muntedpissmole/pccs5/images/ipad_glassmorphism_dark_home_portrait.png

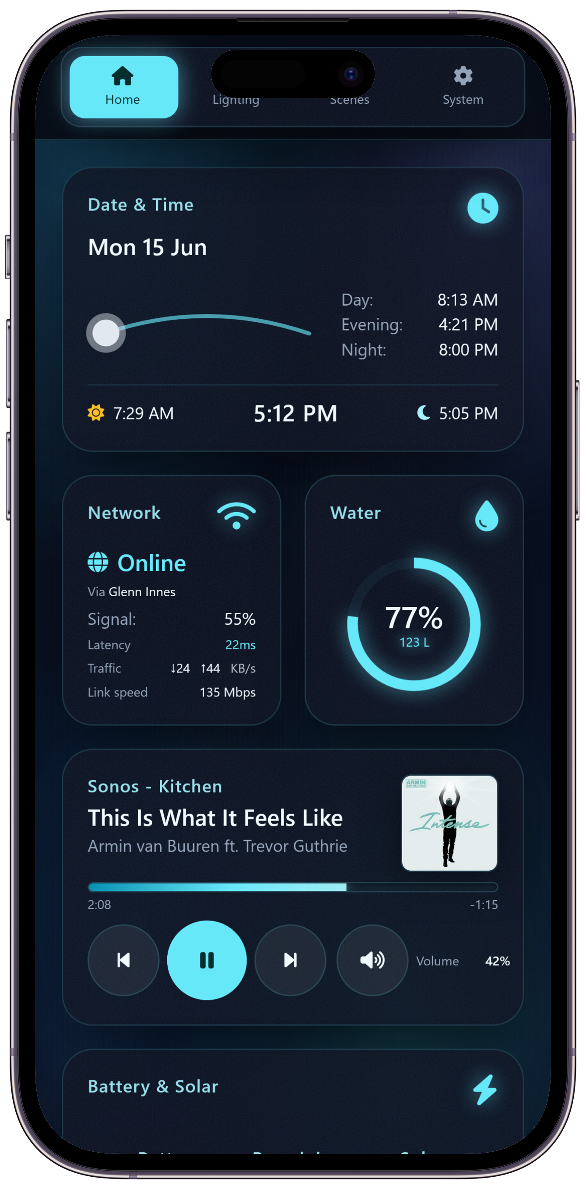
images/ipad_glassmorphism_dark_home_portrait.png
