muntedpissmole/pccs5/images/ipad_glassmorphism_light_home_landscape.png

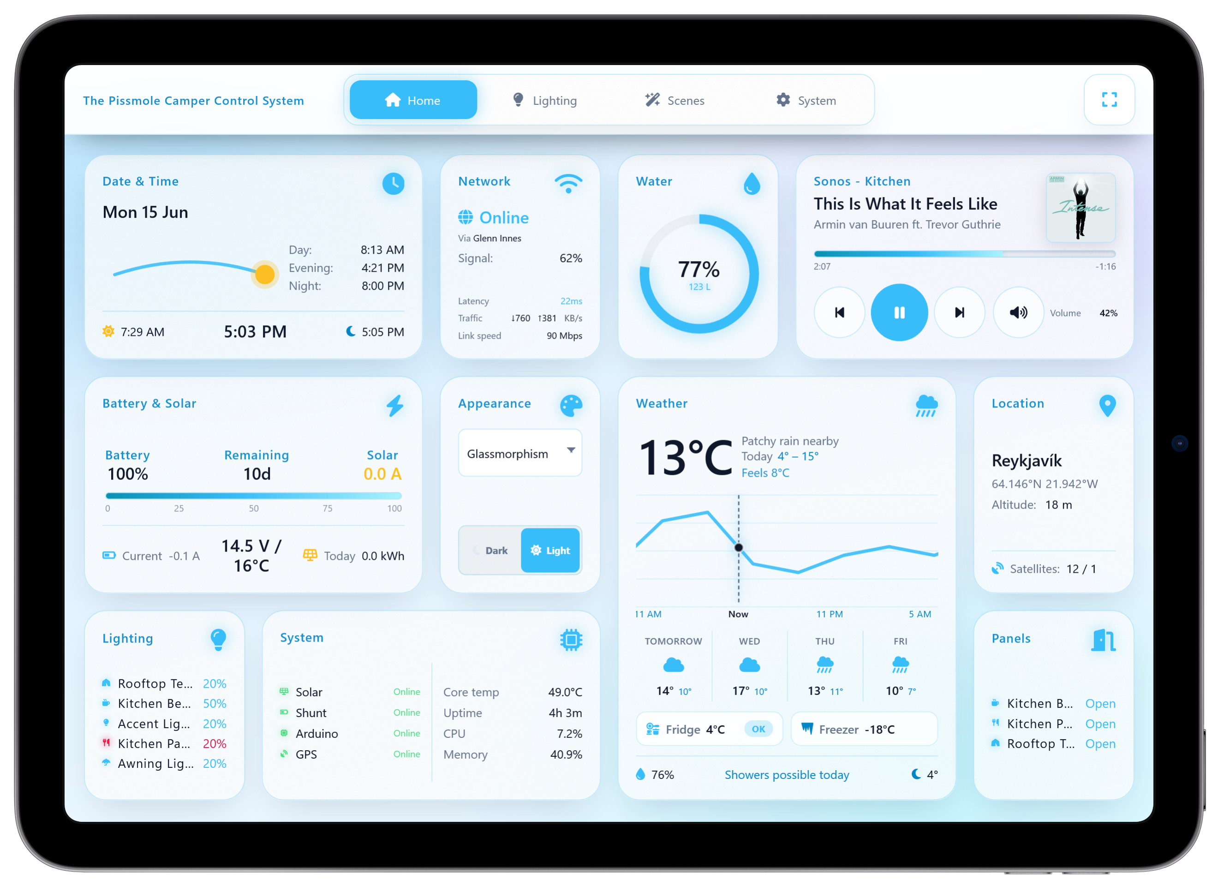
images/ipad_glassmorphism_light_home_landscape.png
