muntedpissmole/pccs5/images/ipad_glassmorphism_light_lighting_landscape.png

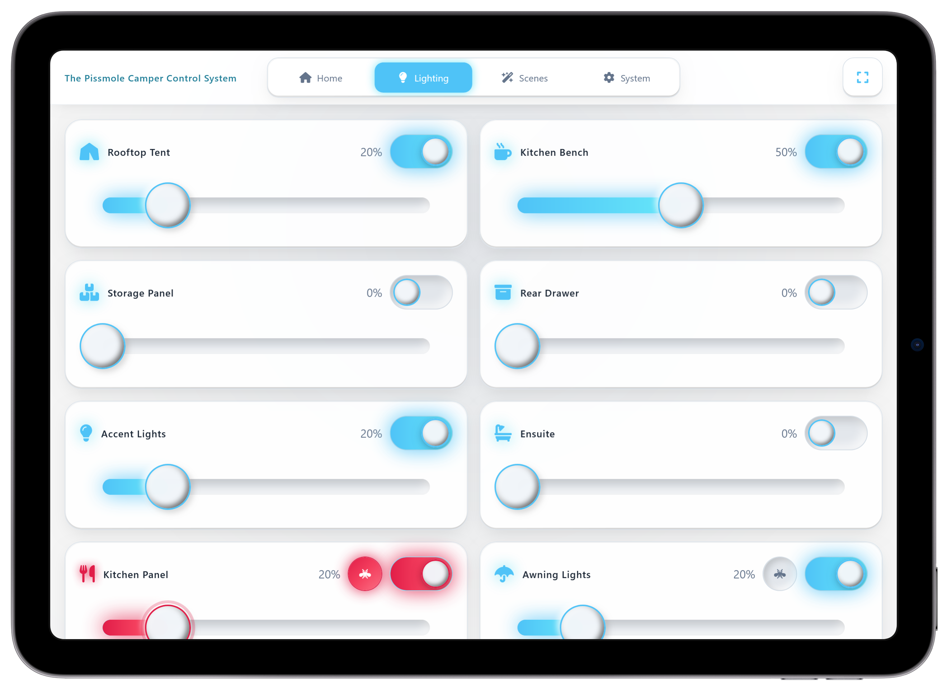
images/ipad_glassmorphism_light_lighting_landscape.png
