muntedpissmole/pccs5/images/ipad_neumorphism_dark_system_landscape.png

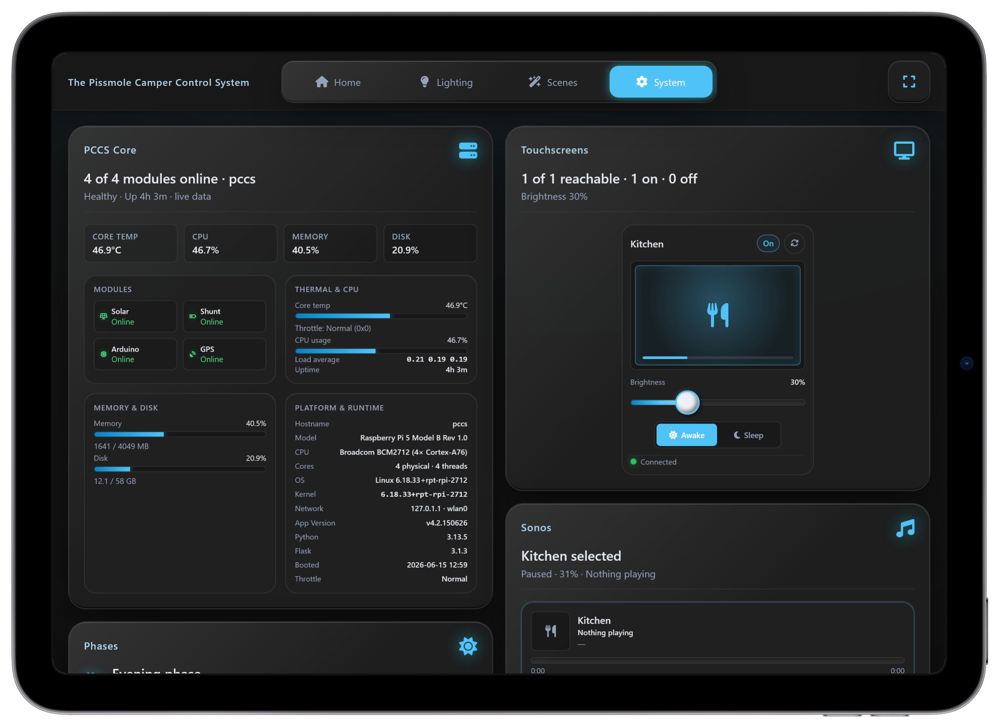
images/ipad_neumorphism_dark_system_landscape.png
