muntedpissmole/pccs5/images/themes/Claymorphism/Screen Shot 2026-06-15 at 17.03.54.png

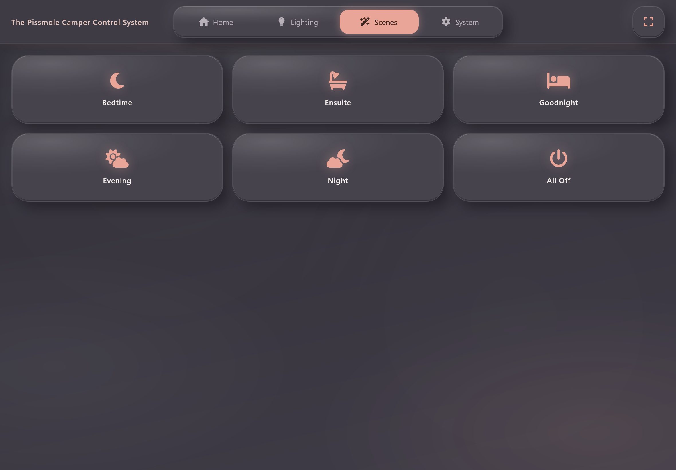
images/themes/Claymorphism/Screen Shot 2026-06-15 at 17.03.54.png
