muntedpissmole/pccs5/images/themes/Cyberpunk/Screen Shot 2026-06-15 at 17.04.39.png

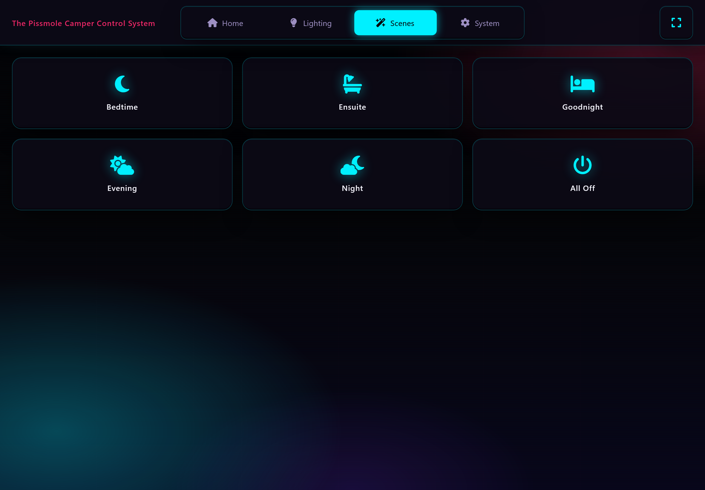
images/themes/Cyberpunk/Screen Shot 2026-06-15 at 17.04.39.png
