muntedpissmole/pccs5/images/themes/Ember/Screen Shot 2026-06-15 at 17.05.40.png

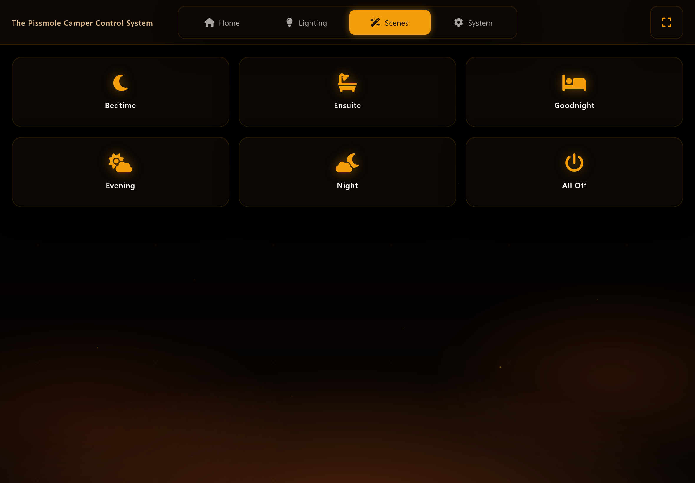
images/themes/Ember/Screen Shot 2026-06-15 at 17.05.40.png
