muntedpissmole/pccs5/images/themes/Glassmorphism/Screen Shot 2026-06-15 at 17.03.24.png

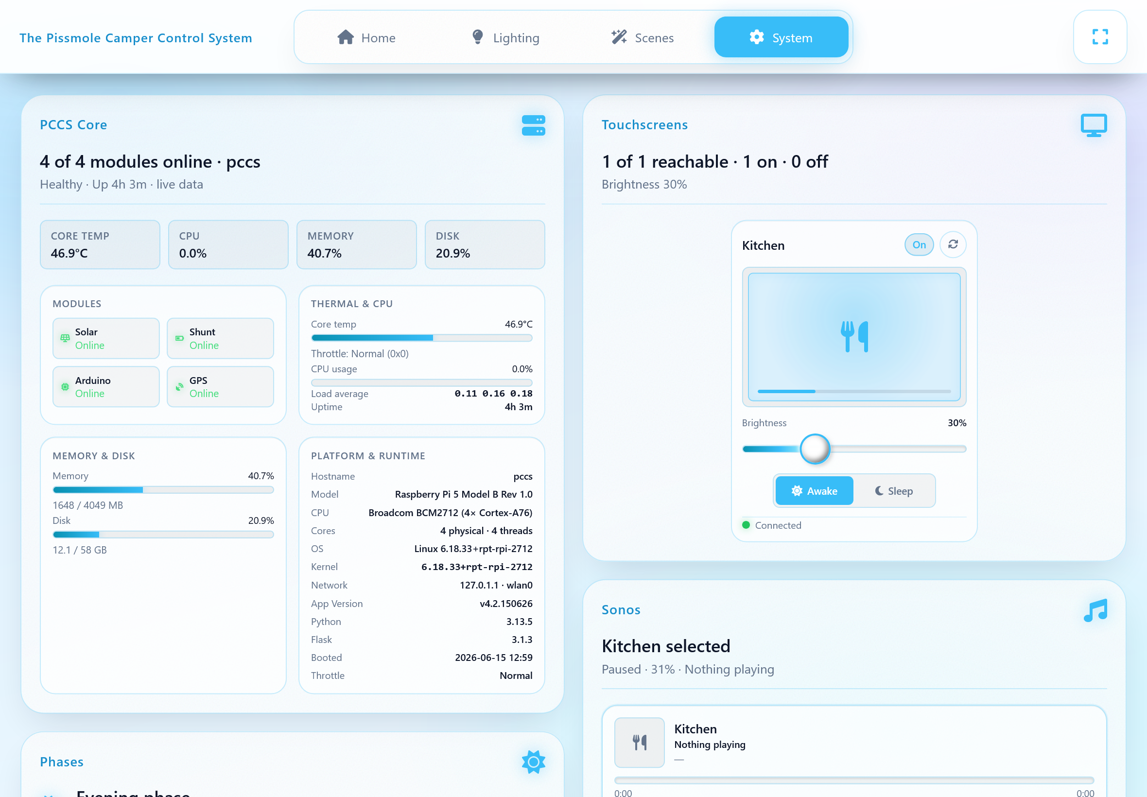
images/themes/Glassmorphism/Screen Shot 2026-06-15 at 17.03.24.png
