muntedpissmole/pccs5/images/themes/Industrial/Screen Shot 2026-06-15 at 17.06.28.png

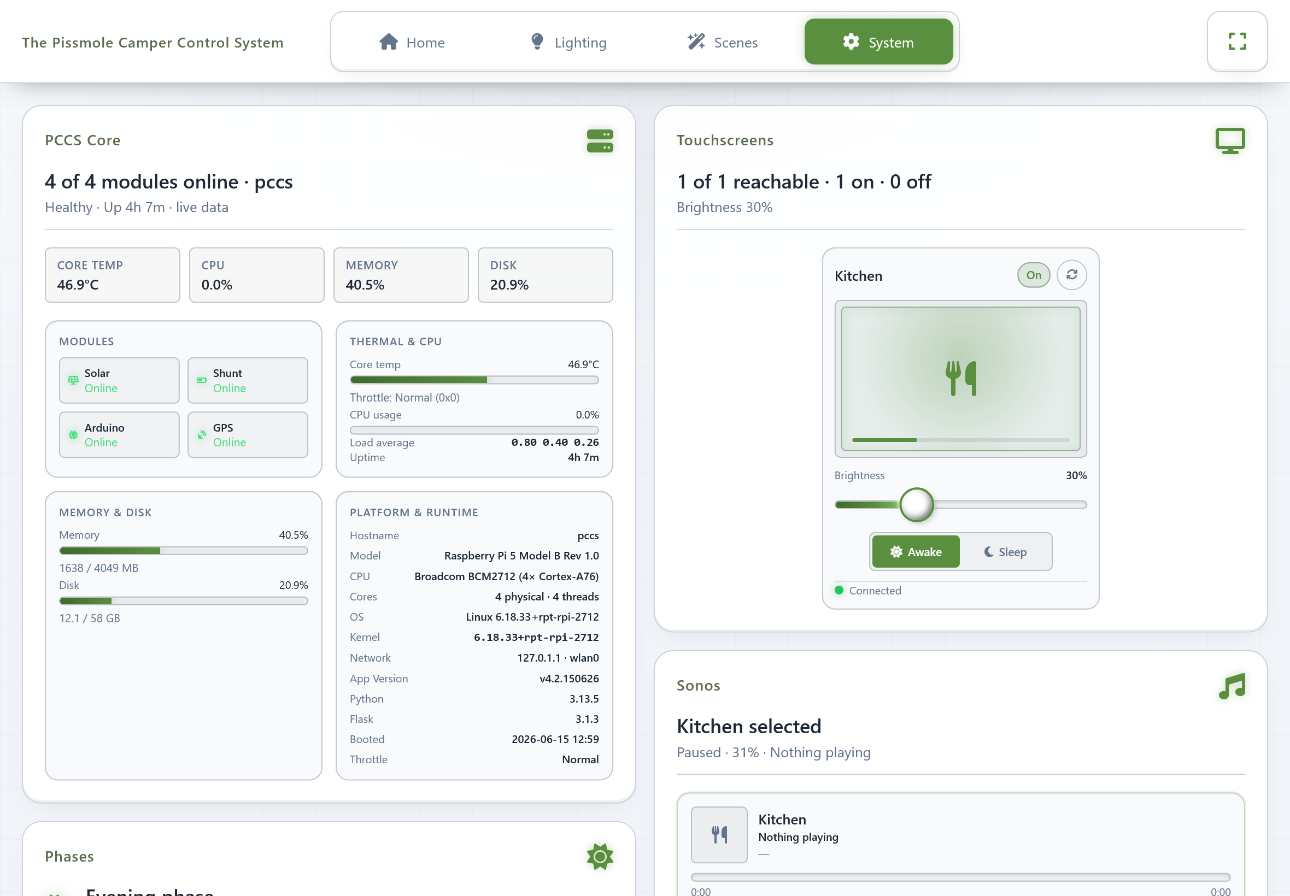
images/themes/Industrial/Screen Shot 2026-06-15 at 17.06.28.png
