muntedpissmole/pccs5/images/themes/Nebula/Screen Shot 2026-06-15 at 17.06.52.png

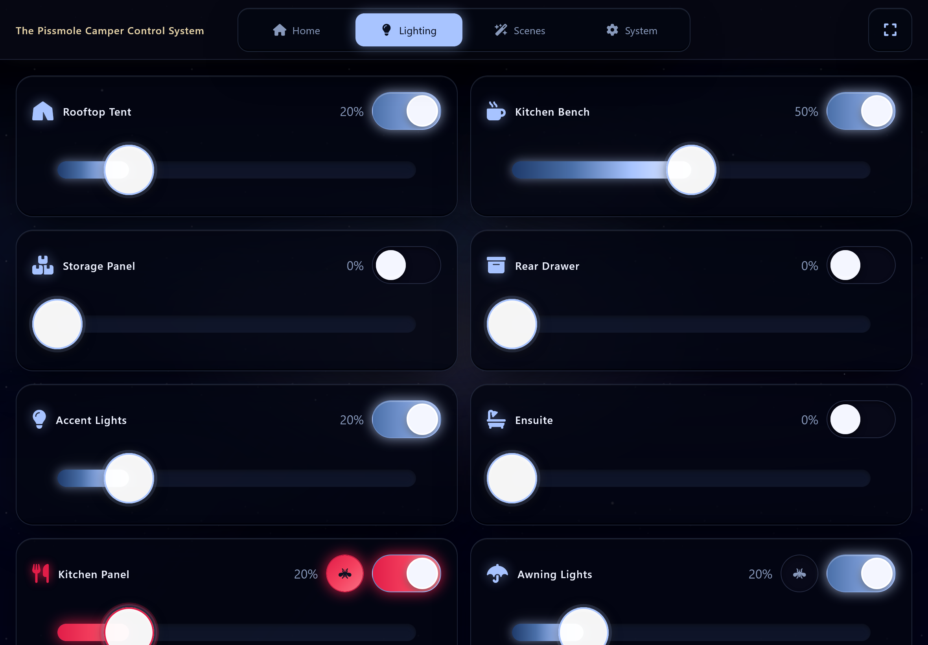
images/themes/Nebula/Screen Shot 2026-06-15 at 17.06.52.png
