muntedpissmole/pccs5/images/themes/Nebula/Screen Shot 2026-06-15 at 17.07.05.png

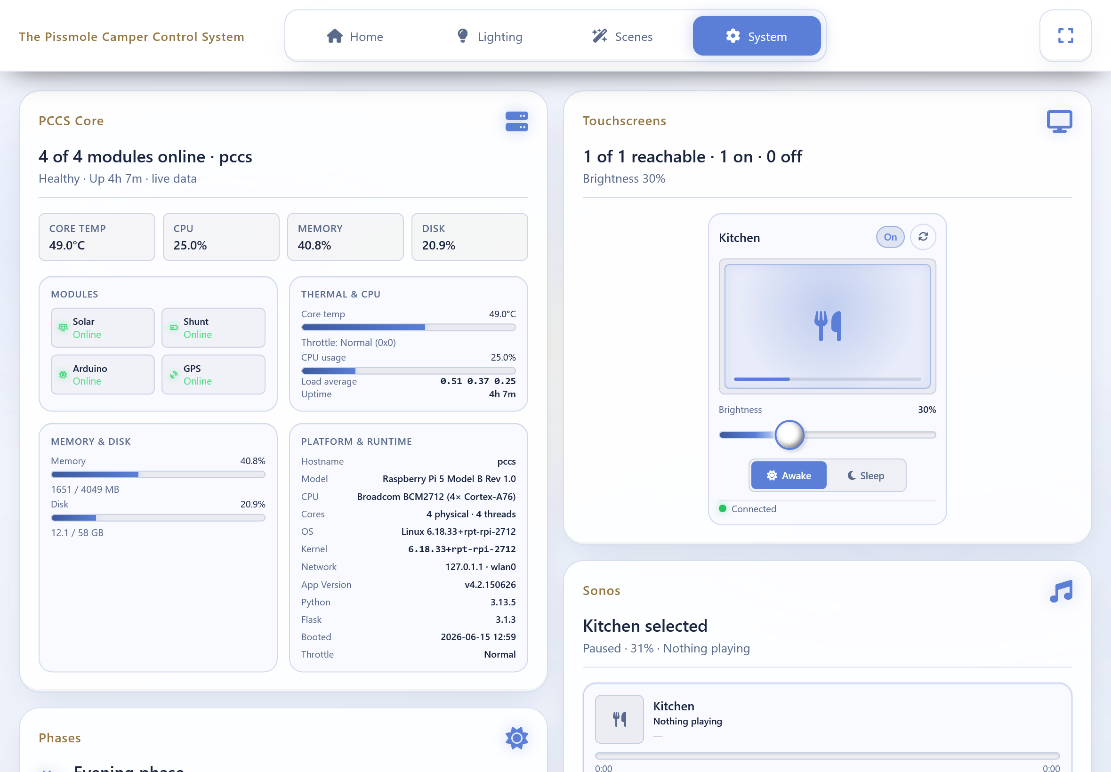
images/themes/Nebula/Screen Shot 2026-06-15 at 17.07.05.png
