muntedpissmole/pccs5/images/themes/Neumorphism/Screen Shot 2026-06-15 at 17.02.20.png

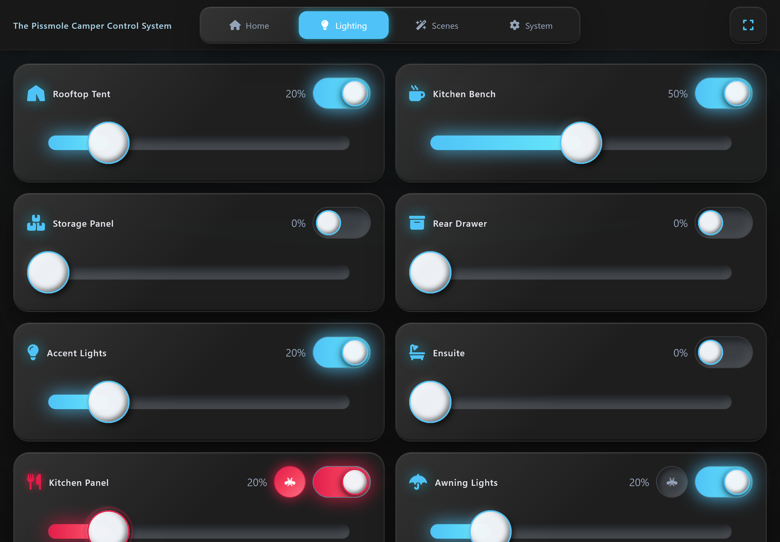
images/themes/Neumorphism/Screen Shot 2026-06-15 at 17.02.20.png
