muntedpissmole/pccs5/images/themes/Obsidian/Screen Shot 2026-06-15 at 17.07.49.png

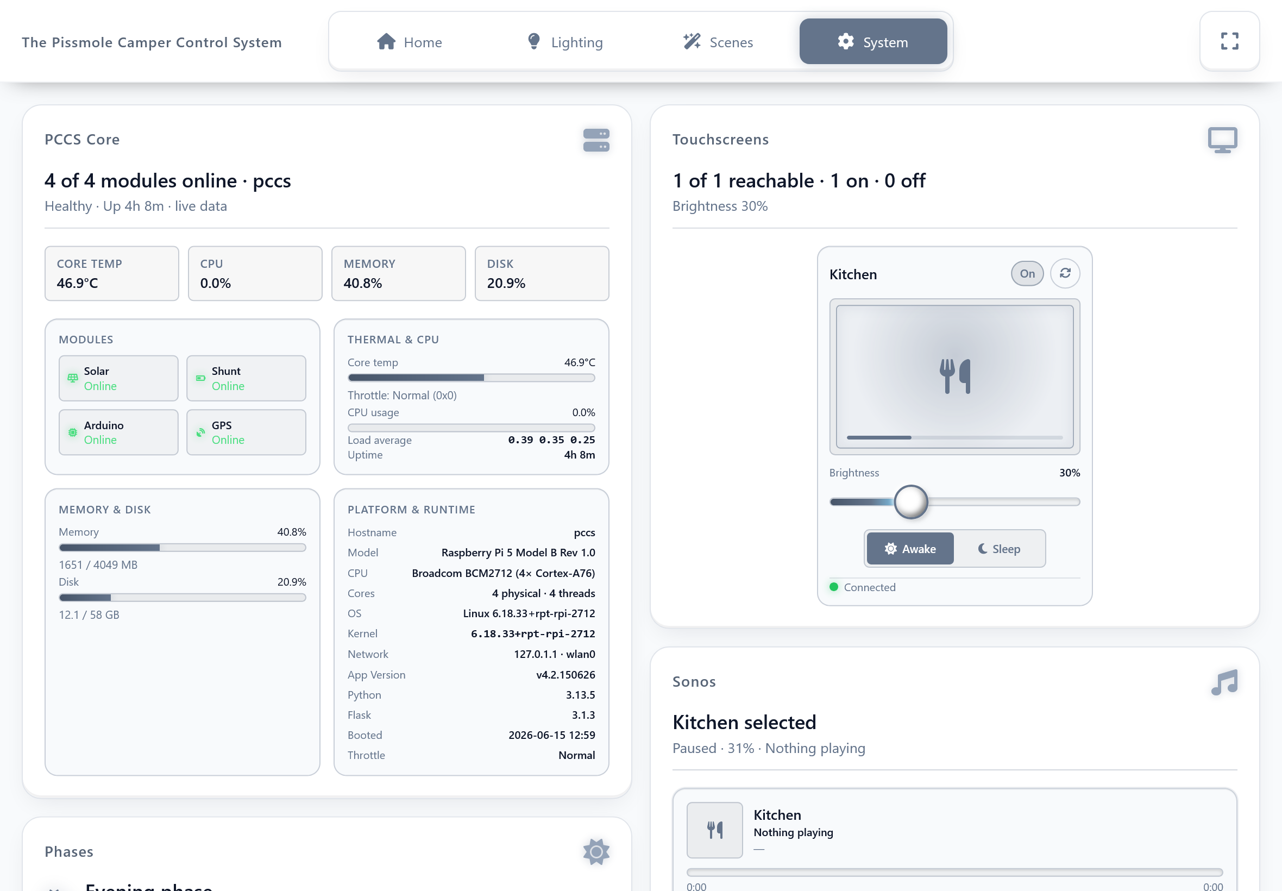
images/themes/Obsidian/Screen Shot 2026-06-15 at 17.07.49.png
