muntedpissmole/pccs5/images/themes/Terminal/Screen Shot 2026-06-15 at 17.09.07.png

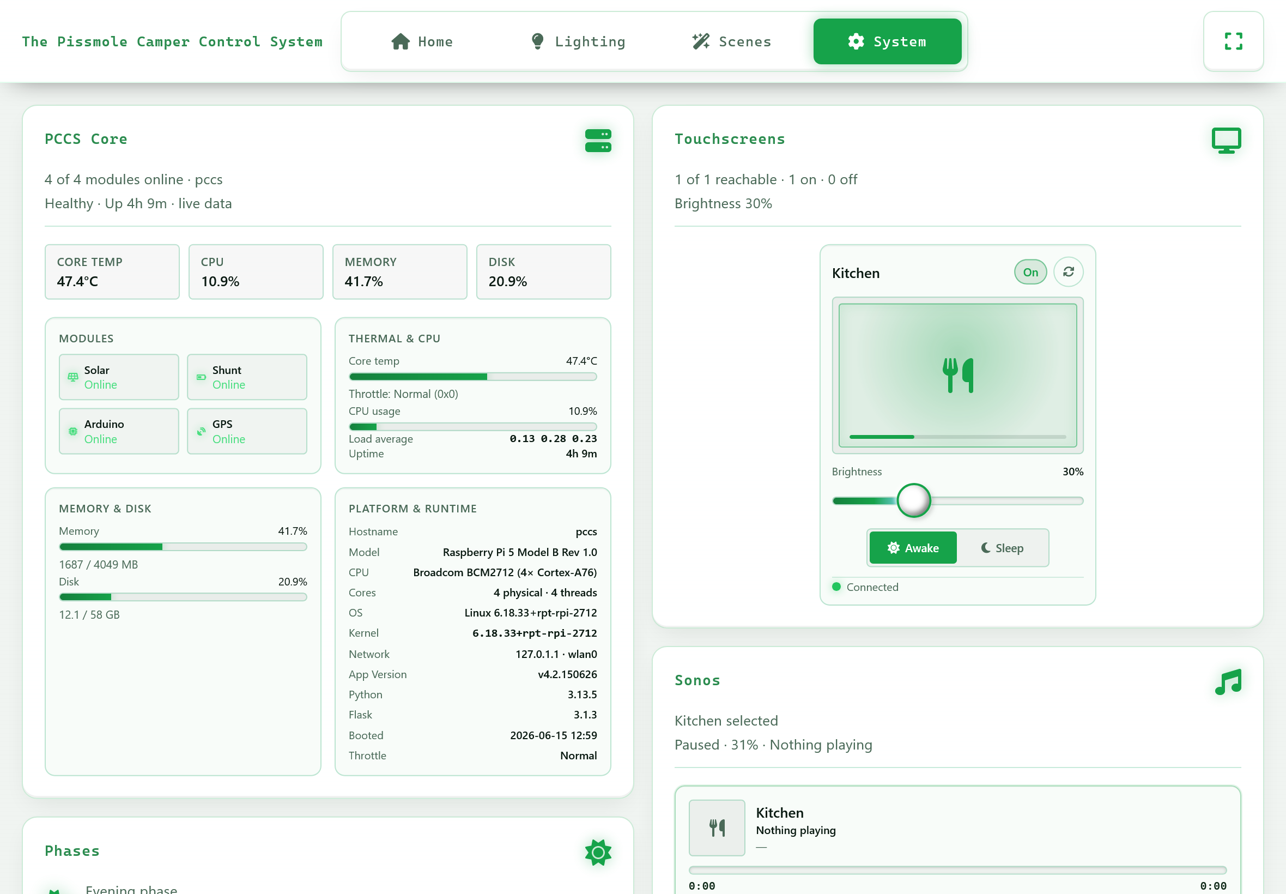
images/themes/Terminal/Screen Shot 2026-06-15 at 17.09.07.png
