muntedpissmole/pccs5/images/themes/Void/Screen Shot 2026-06-15 at 17.09.32.png

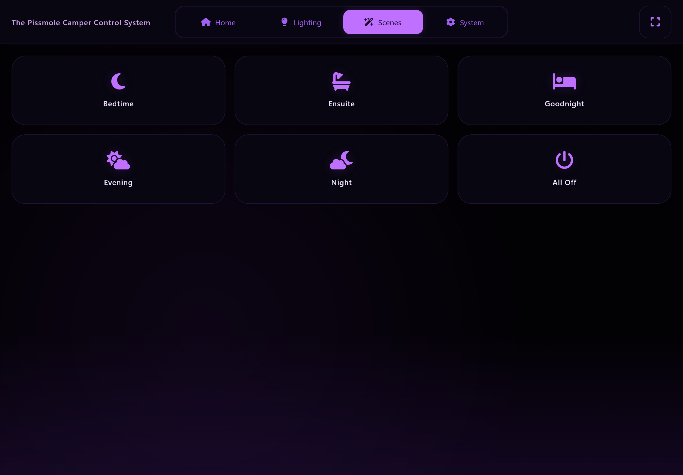
images/themes/Void/Screen Shot 2026-06-15 at 17.09.32.png
