muntedpissmole/pccs5/static/images/kse-this-consequence.jpg

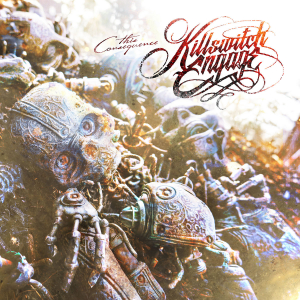
static/images/kse-this-consequence.jpg
