muntedpissmole/pccs5/kicad/analog_inputs.kicad_sch

## KiCad design kicad/analog_inputs.kicad_sch (2026-08-07)

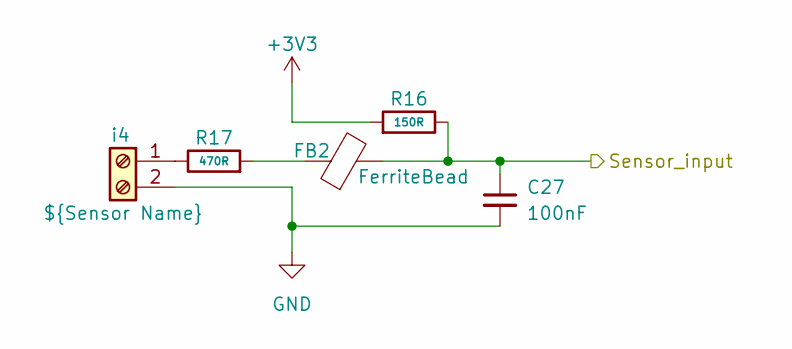
[picture p79: schematic analog_inputs.kicad_sch]

Parts:
C27: 100nF; C_0603_1608Metric; LCSC Part # C1590
FB2: FerriteBead; L_0603_1608Metric; LCSC Part # C1002
R16: 150R; R_0805_2012Metric; LCSC Part # C17471
R17: 470R; R_0805_2012Metric; LCSC Part # C17710
i4: ${Sensor Name}; TerminalBlock_Phoenix_MKDS-1,5-2-5.08_1x02_P5.08mm_Horizont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; LCSC Part # C8445

Connections:
+3V3: R16.2
GND: C27.2, i4.2
unnamed: FB2.1, R17.2
unnamed: R17.1, i4.1
Sensor_input: C27.1, FB2.2, R16.1
