muntedpissmole/pccs5/kicad/esp32.kicad_sch

## KiCad design kicad/esp32.kicad_sch (2026-08-07)

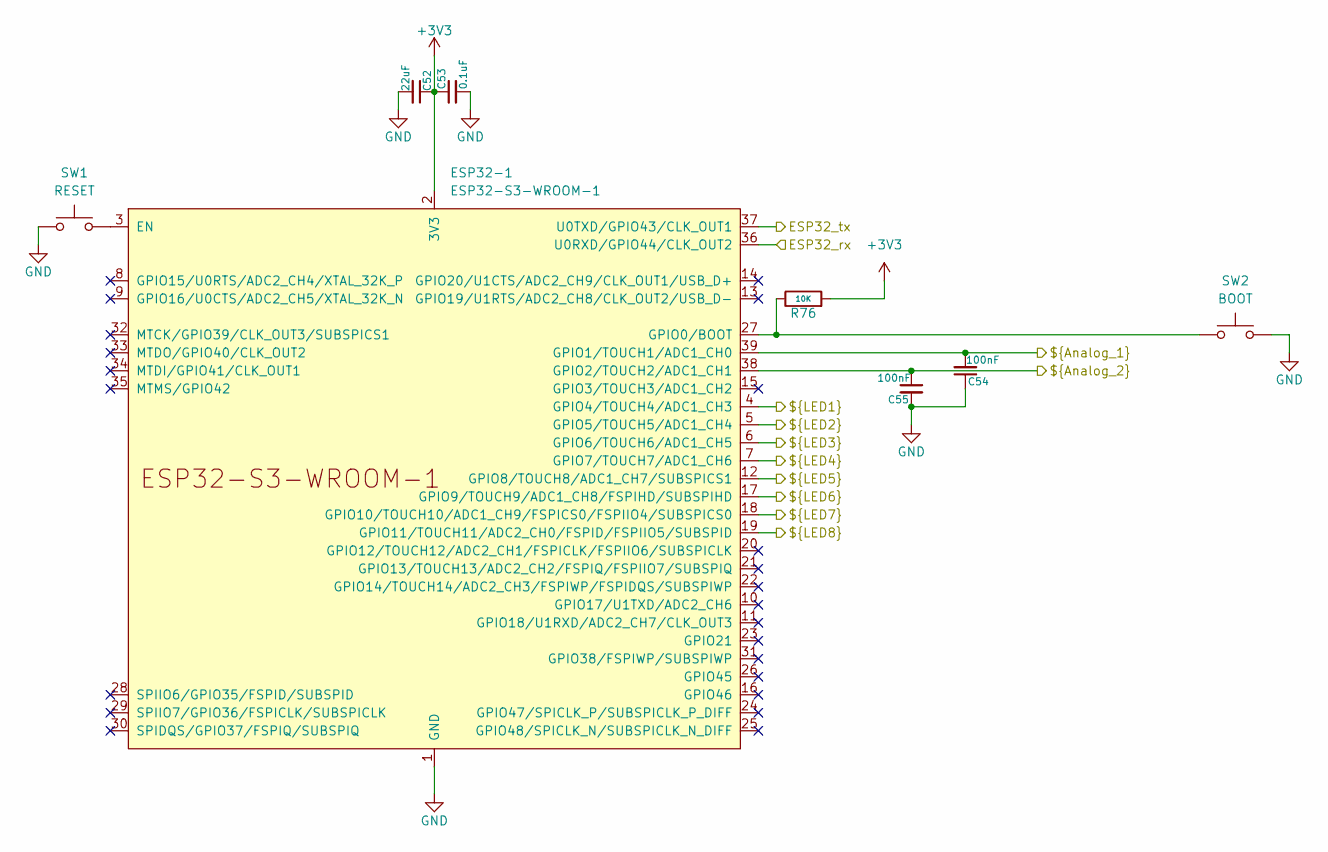
[picture p80: schematic esp32.kicad_sch]

Parts:
C52: 22uF; C_0805_2012Metric; LCSC Part # C86816
C53: 0.1uF; C_0805_2012Metric; LCSC Part # C86041
C54, C55: 100nF; C_0402_1005Metric; LCSC Part # C60474
ESP32-1: ESP32-S3-WROOM-1; ESP32-S3-WROOM-1U; LCSC Part # C3013946
R76: 10K; R_0402_1005Metric; LCSC Part # C60490
SW1: RESET; SW_PUSH_1P1T_6x3.5mm_H5.0_APEM_MJTP1250; LCSC Part # C500070
SW2: BOOT; SW_PUSH_1P1T_6x3.5mm_H5.0_APEM_MJTP1250; LCSC Part # C500070

Connections:
${Analog_1}: C54.2, ESP32-1.39 (GPIO1/TOUCH1/ADC1_CH0)
${Analog_2}: C55.1, ESP32-1.38 (GPIO2/TOUCH2/ADC1_CH1)
${LED1}: ESP32-1.4 (GPIO4/TOUCH4/ADC1_CH3)
${LED2}: ESP32-1.5 (GPIO5/TOUCH5/ADC1_CH4)
${LED3}: ESP32-1.6 (GPIO6/TOUCH6/ADC1_CH5)
${LED4}: ESP32-1.7 (GPIO7/TOUCH7/ADC1_CH6)
${LED5}: ESP32-1.12 (GPIO8/TOUCH8/ADC1_CH7/SUBSPICS1)
${LED6}: ESP32-1.17 (GPIO9/TOUCH9/ADC1_CH8/FSPIHD/SUBSPIHD)
${LED7}: ESP32-1.18 (GPIO10/TOUCH10/ADC1_CH9/FSPICS0/FSPIIO4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)
${LED8}: ESP32-1.19 (GPIO11/TOUCH11/ADC2_CH0/FSPID/FSPIIO5/S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)
+3V3: C52.1, C53.1, ESP32-1.2 (3V3), R76.2
ESP32_rx: ESP32-1.36 (U0RXD/GPIO44/CLK_OUT2)
ESP32_tx: ESP32-1.37 (U0TXD/GPIO43/CLK_OUT1)
GND: C52.2, C53.2, C54.1, C55.2, ESP32-1.1 (GND), ESP32-1.40 (GND), ESP32-1.41 (GND), SW1.1, SW2.1
unnamed: ESP32-1.3 (EN), SW1.2
unnamed: ESP32-1.27 (GPIO0/BOOT), R76.1, SW2.2
