muntedpissmole/pccs5/kicad/led_channel.kicad_sch

## KiCad design kicad/led_channel.kicad_sch (2026-08-07)

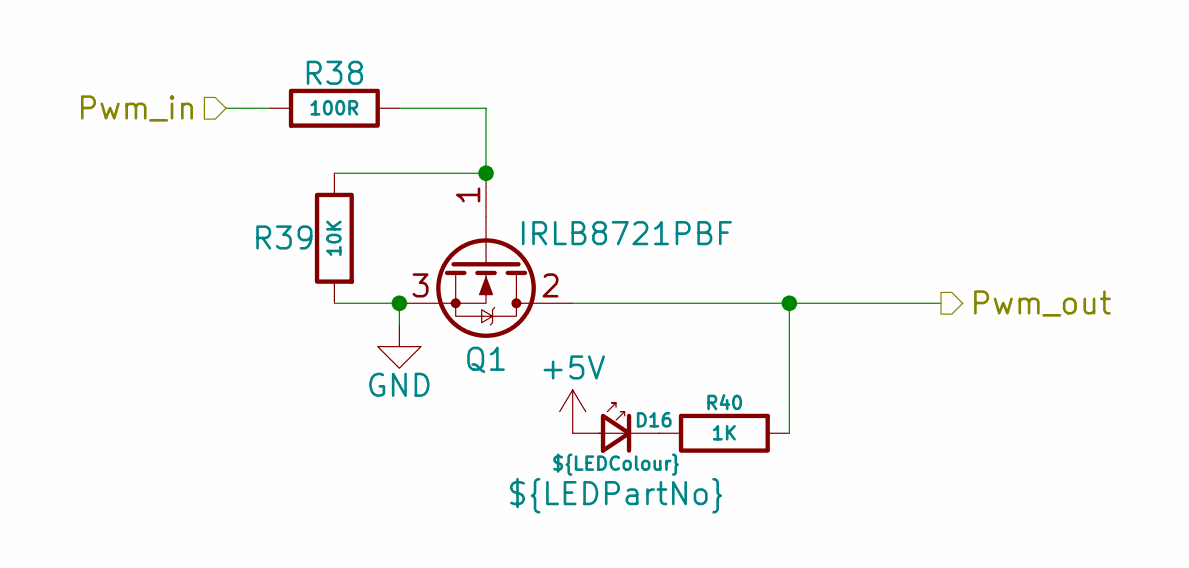
[picture p81: schematic led_channel.kicad_sch]

Parts:
D16: ${LEDColour}; LED_0603_1608Metric; LCSC Part # ${LEDPartNo}
Q1: IRLB8721PBF; TO-252-2; LCSC Part # C99124
R38: 100R; R_0805_2012Metric; LCSC Part # C17408
R39: 10K; R_0805_2012Metric; LCSC Part # C17414
R40: 1K; R_0805_2012Metric; LCSC Part # C17513

Connections:
+5V: D16.2 (A)
GND: Q1.3 (S), R39.2
unnamed: D16.1 (K), R40.1
unnamed: Q1.1 (G), R38.1, R39.1
Pwm_in: R38.2
Pwm_out: Q1.2 (D), R40.2
