muntedpissmole/pccs5/kicad/led_power.kicad_sch

## KiCad design kicad/led_power.kicad_sch (2026-08-07)

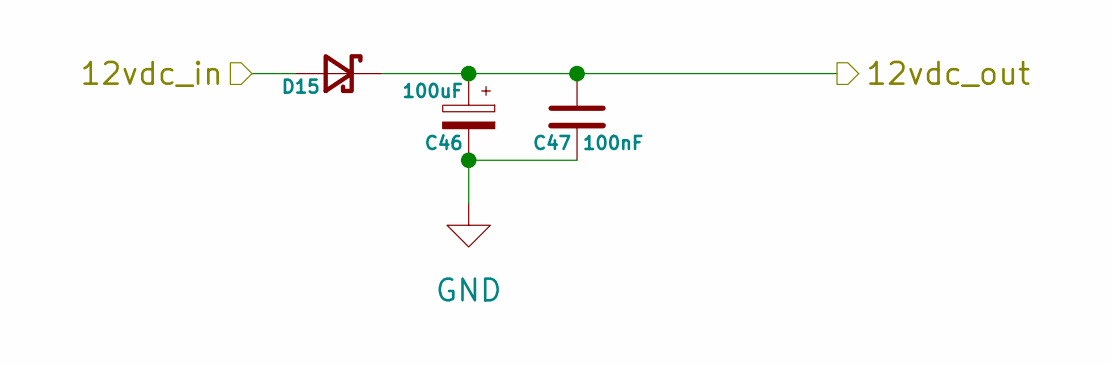
[picture p82: schematic led_power.kicad_sch]

Parts:
C46: 100uF; CP_Radial_D6.3mm_P2.50mm; LCSC Part # C44587
C47: 100nF; C_0805_2012Metric; LCSC Part # C49678
D15: D_PowerDI-5; LCSC Part # C2759901

Connections:
12vdc_in: D15.2 (A)
12vdc_out: C46.1, C47.1, D15.1 (K)
GND: C46.2, C47.2
