muntedpissmole/pccs5/kicad/reed_input.kicad_sch

## KiCad design kicad/reed_input.kicad_sch (2026-08-07)

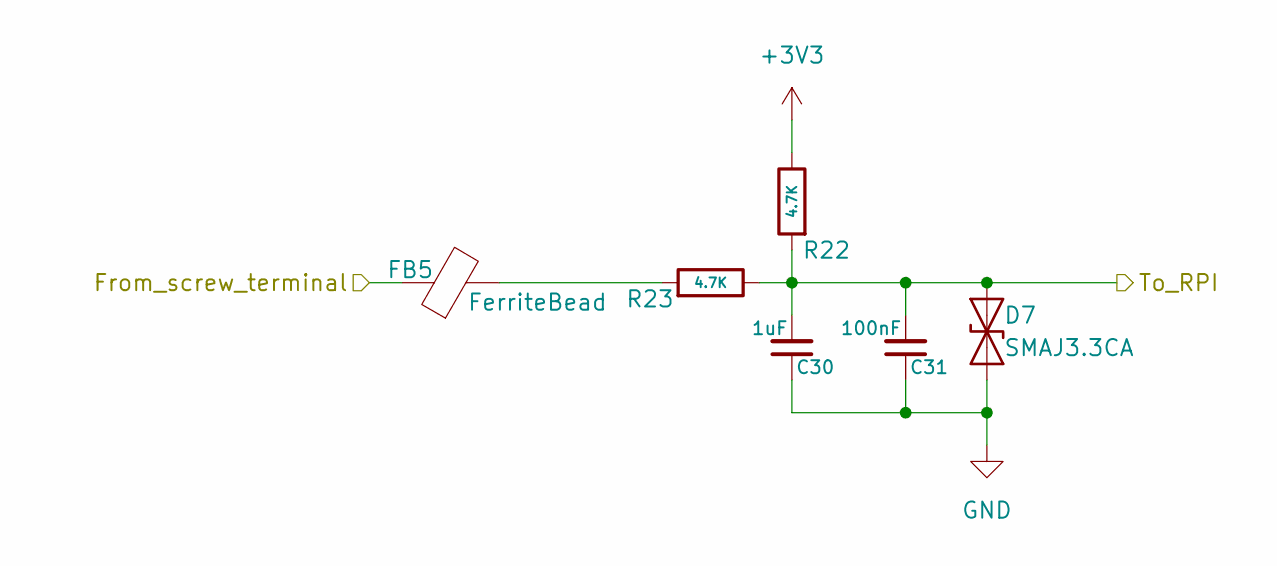
[picture p85: schematic reed_input.kicad_sch]

Parts:
C30: 1uF; C_0805_2012Metric; LCSC Part # C91185
C31: 100nF; C_0805_2012Metric; LCSC Part # C49678
D7: SMAJ3.3CA; D_SMA; LCSC Part # C18199545
FB5: FerriteBead; L_0603_1608Metric; LCSC Part # C1002
R22, R23: 4.7K; R_0805_2012Metric; LCSC Part # C17673

Connections:
+3V3: R22.1
From_screw_terminal: FB5.1
GND: C30.1, C31.1, D7.1 (A1)
unnamed: FB5.2, R23.2
To_RPI: C30.2, C31.2, D7.2 (A2), R22.2, R23.1
