muntedpissmole/pccs5/kicad/relay_channel.kicad_sch

## KiCad design kicad/relay_channel.kicad_sch (2026-08-07)

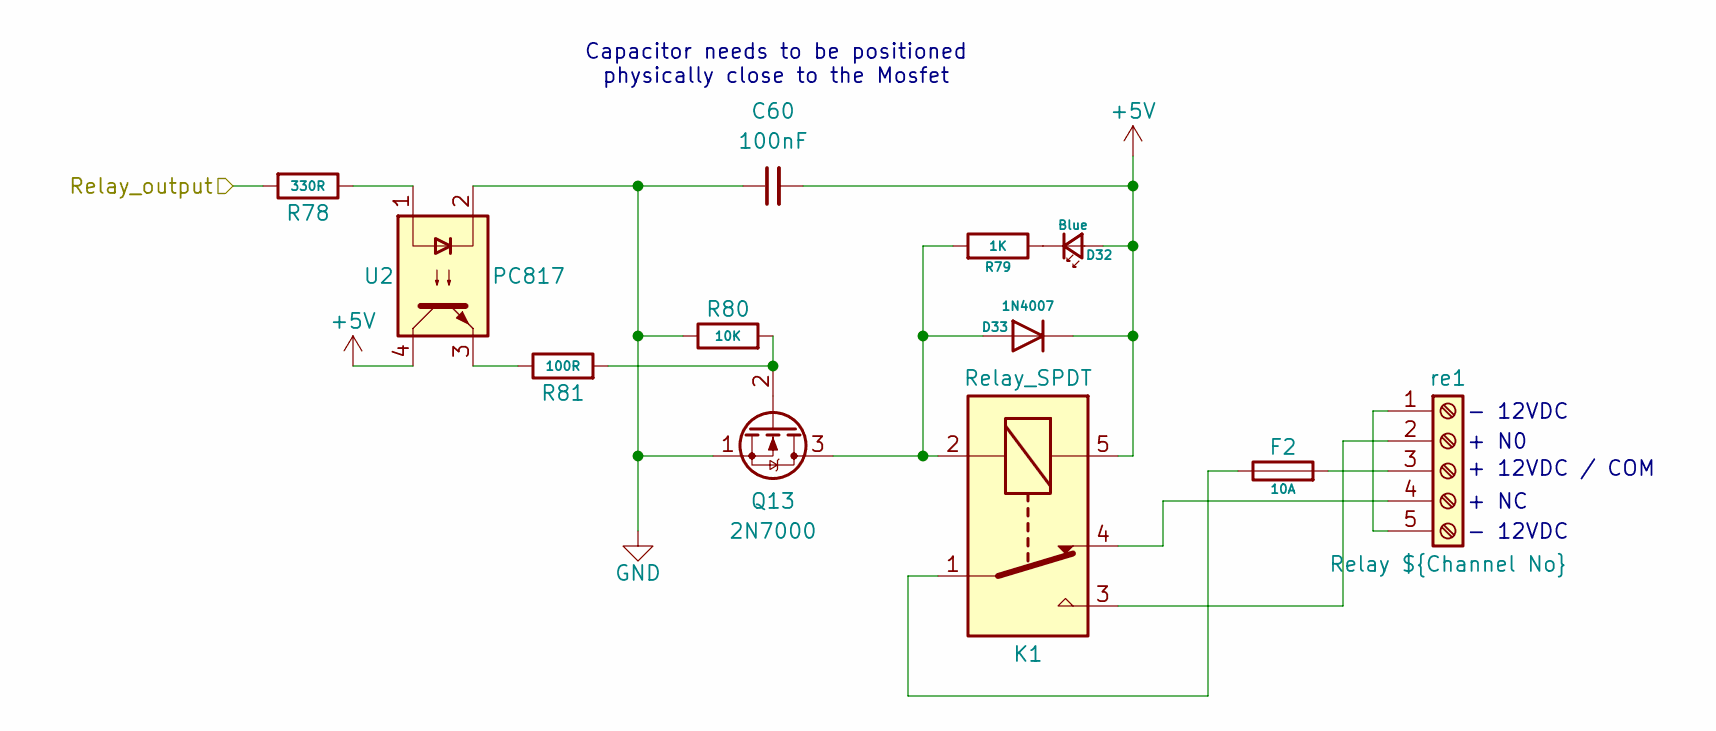
[picture p86: schematic relay_channel.kicad_sch]

Parts:
C60: 100nF; C_0805_2012Metric; LCSC Part # C49678
D32: Blue; LED_0603_1608Metric; LCSC Part # C2288
D33: 1N4007; D_SMA; LCSC Part # C64915
F2: 10A; Fuse_Bourns_MF-RG1000; LCSC Part # C14767
K1: Relay_SPDT; Relay_SPDT_SANYOU_SRD_Series_Form_C; LCSC Part # C35449
Q13: 2N7000; TO-92_Inline; LCSC Part # C9114
R78: 330R; R_0805_2012Metric; LCSC Part # C17630
R79: 1K; R_0603_1608Metric; LCSC Part # C5123612
R80: 10K; R_0805_2012Metric; LCSC Part # C17414
R81: 100R; R_0805_2012Metric; LCSC Part # C17408
U2: PC817; DIP-4_W7.62mm; LCSC Part # C5353
re1: Relay ${Channel No}; TerminalBlock_Phoenix_MKDS-3-5-5.08_1x05_P5.08mm_Horizontal; LCSC Part # C8423

Connections:
+5V: C60.2, D32.2 (A), D33.1 (K), K1.5, U2.4
GND: C60.1, Q13.1 (S), R80.1, U2.2
unnamed: D32.1 (K), R79.1
unnamed: D33.2 (A), K1.2, Q13.3 (D), R79.2
unnamed: F2.1, K1.1
unnamed: F2.2, re1.3
unnamed: K1.3, re1.2
unnamed: K1.4, re1.4
unnamed: Q13.2 (G), R80.2, R81.2
unnamed: R78.1, U2.1
unnamed: R81.1, U2.3
unnamed: re1.1, re1.5
Relay_output: R78.2

Notes on the sheet:
+ NC
+ N0
+ 12VDC / COM
- 12VDC
Capacitor needs to be positioned physically close to the Mosfet
