muntedpissmole/pccs5/kicad/ws2815.kicad_sch

## KiCad design kicad/ws2815.kicad_sch (2026-08-07)

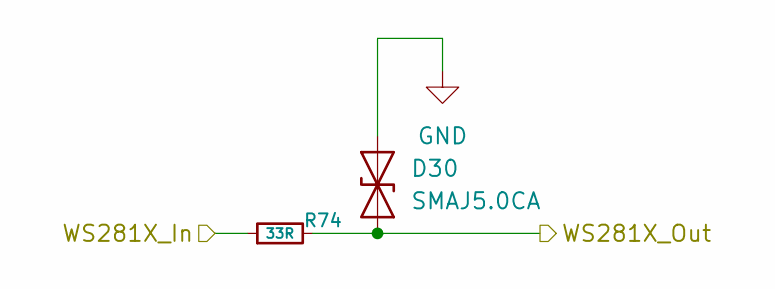
[picture p87: schematic ws2815.kicad_sch]

Parts:
D30: SMAJ5.0CA; D_SMA; LCSC Part # C78402
R74: 33R; R_0805_2012Metric; LCSC Part # C17634

Connections:
GND: D30.1 (A1)
WS281X_In: R74.1
WS281X_Out: D30.2 (A2), R74.2
